rasteri/SC1000/software/midi.c

/*
 * Copyright (C) 2018 Mark Hills <mark@xwax.org>
 *
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
 */

#include <stdio.h>
#include <string.h>

#include "midi.h"

int listdev(char *devname, char names[64][64])

{

    char** hints;
    int    err;
    char** n;
    char*  name;

    int num = 0;


    /* Enumerate sound devices */
    err = snd_device_name_hint(-1, devname, (void***)&hints);
    if (err != 0) {

        fprintf(stderr, "*** Cannot get device names\n");
        exit(1);

    }

    n = hints;
    while (*n != NULL) {

        name = snd_device_name_get_hint(*n, "NAME");

        strcpy(names[num++], name);

        printf("Name of device: %s\n", name);

        if (name && strcmp("null", name)) free(name);
	printf("lots\n");
        n++;

    }

    //Free hint buffer too
    snd_device_name_free_hint((void**)hints);
    return num;
	return 0;

}

/*
 * Print error code from ALSA
 */

static void alsa_error(const char *msg, int r)
{
    fprintf(stderr, "ALSA %s: %s\n", msg, snd_strerror(r));
}

int midi_open(struct midi *m, const char *name)
{
    int r;

    r = snd_rawmidi_open(&m->in, &m->out, name, SND_RAWMIDI_NONBLOCK);
    if (r < 0)
    {
        alsa_error("rawmidi_open", r);
        return -1;
    }

    return 0;
}

void midi_close(struct midi *m)
{
    if (snd_rawmidi_close(m->in) < 0)
        abort();
    if (snd_rawmidi_close(m->out) < 0)
        abort();
}

/*
 * Get the poll descriptors for reading on this MIDI device
 *
 * Pre: len is maximum size of array pe
 * Return: -1 if len is not large enough, otherwise n on success
 * Post: on success, pe is filled with n entries
 */

ssize_t midi_pollfds(struct midi *m, struct pollfd *pe, size_t len)
{
    int r;

    if (snd_rawmidi_poll_descriptors_count(m->in) > len)
        return -1;

    r = snd_rawmidi_poll_descriptors(m->in, pe, len);
    assert(r >= 0);

    return r;
}

/*
 * Read raw bytes of input
 *
 * Pre: len is maximum size of buffer
 * Return: -1 on error, otherwise n on success
 * Post: on success, buf is filled with n bytes of data
 */

ssize_t midi_read(struct midi *m, void *buf, size_t len)
{
    int r;

    r = snd_rawmidi_read(m->in, buf, len);
    if (r < 0)
    {
        if (r == -EAGAIN)
            return 0;
        alsa_error("rawmidi_read", r);
        return -1;
    }

    return r;
}

ssize_t midi_write(struct midi *m, const void *buf, size_t len)
{
    int r;

    r = snd_rawmidi_write(m->out, buf, len);
    if (r < 0)
    {
        if (r == -EAGAIN)
            return 0;
        alsa_error("rawmidi_write", r);
        return -1;
    }

    return r;
}
