rasteri/SC1000/software/xwax.h

/*
 * Copyright (C) 2018 Mark Hills <mark@xwax.org>
 *
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
 */

#ifndef XWAX_H
#define XWAX_H

#include "deck.h"

extern size_t ndeck;
extern struct deck deck[];


typedef struct SC_SETTINGS {

    // output buffer size, probably 256
    int buffersize;

    // sample rate, probably 48000
    int samplerate;
	
	// fader options
	char singleVCA;
	char doublecut;
	char hamster;
 
    // fader thresholds for hysteresis
    int faderopenpoint; // value required to open the fader (when fader is closed)
    int faderclosepoint; // value required to close the fader (when fader is open)

    // delay between iterations of the input loop
    int updaterate;

    // 1 when enabled, 0 when not
    int platterenabled;

    // specifies the ratio of platter movement to sample movement
    // 4096 = 1 second for every platter rotation
    // Default 3072 = 1.33 seconds for every platter rotation
    int platterspeed;


    // How long to debounce external GPIO switches
    int debouncetime;
	
	// How long a button press counts as a hold
    int holdtime;
	
	// Virtual slipmat slippiness - how quickly the sample returns to normal speed after you let go of the jog wheel
	// Higher values are slippier
    int slippiness;

	// How long the the platter takes to stop after you hit a stop button, higher values are longer
	int brakespeed;
	
	// Pitch range of MIDI commands
	int pitchrange;
	
	// How many seconds to wait before initializing MIDI
	int mididelay;

	// whether or not to take input from the volume knobs (sc500 should enable this setting)
	int disablevolumeadc;

    // whether or not to take input from the PIC buttons (sc500 should enable this setting)
	int disablepicbuttons;

    // how much to adjust the volumes when the volume up/down buttons are pressed or held
    double volAmount;
    double volAmountHeld;
	
    // whether or not to reverse the jogwheel
    int jogReverse;
	
	// whether or not the fader cuts the beats
	int cutbeats;
	
	double initialVolume;

    bool midiRemapped;
    bool ioRemapped;


} SC_SETTINGS;

extern SC_SETTINGS scsettings;
#endif
